Mat931/esp32-doorbell-bus-interface/images/2.png

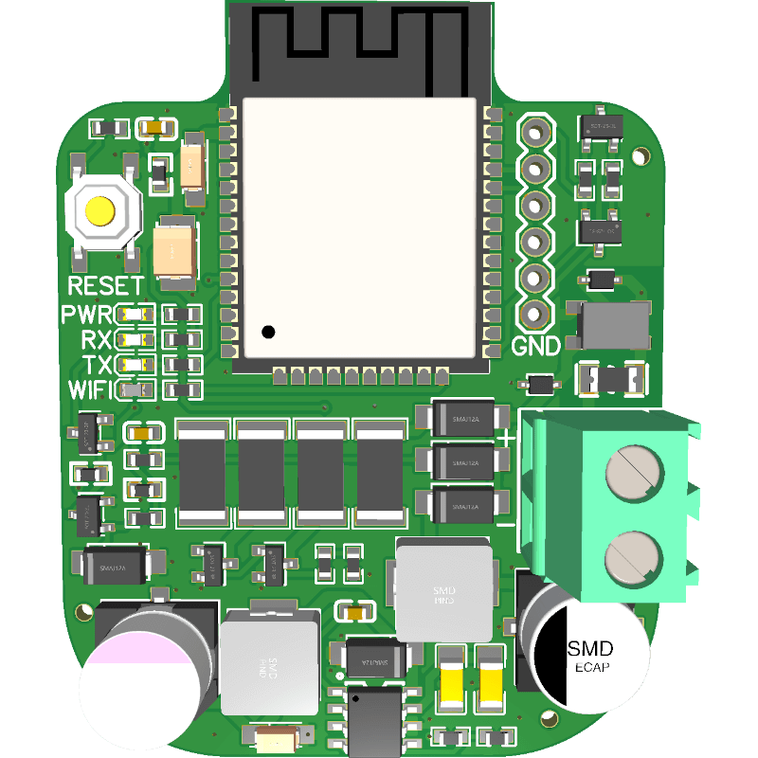
images/2.png
