Mat931/esp32-doorbell-bus-interface/images/3.png

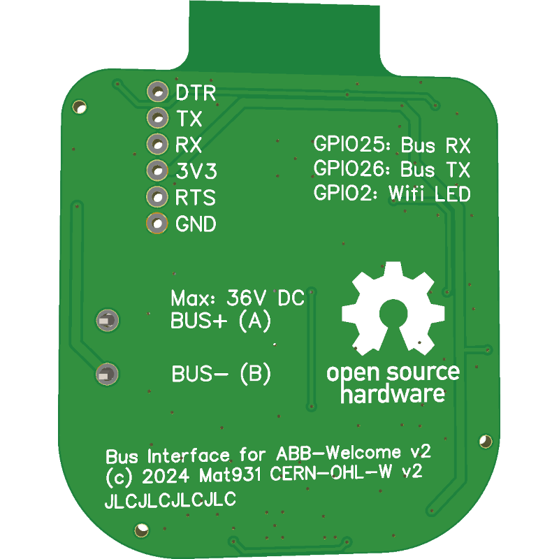
images/3.png
